robori-3dprinter/Mendel/OpenSCAD/prusa-i3-x-idler-1.stl

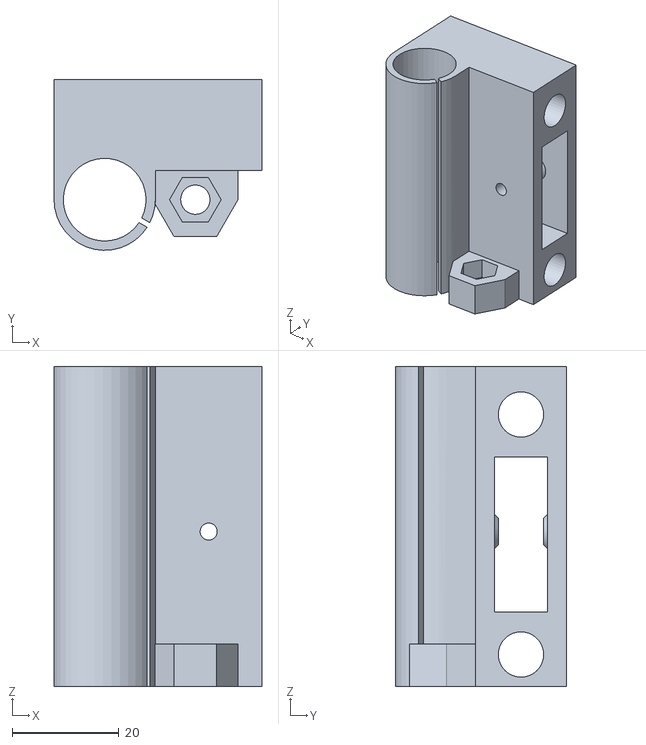
[picture p16: CAD file, 2015-08-26]
OpenSCAD/prusa-i3-x-idler-1.stl
39.0 x 32.0 x 60.0
