robori-3dprinter/Mendel/Printed Part/extruder-tongue-1x.stl

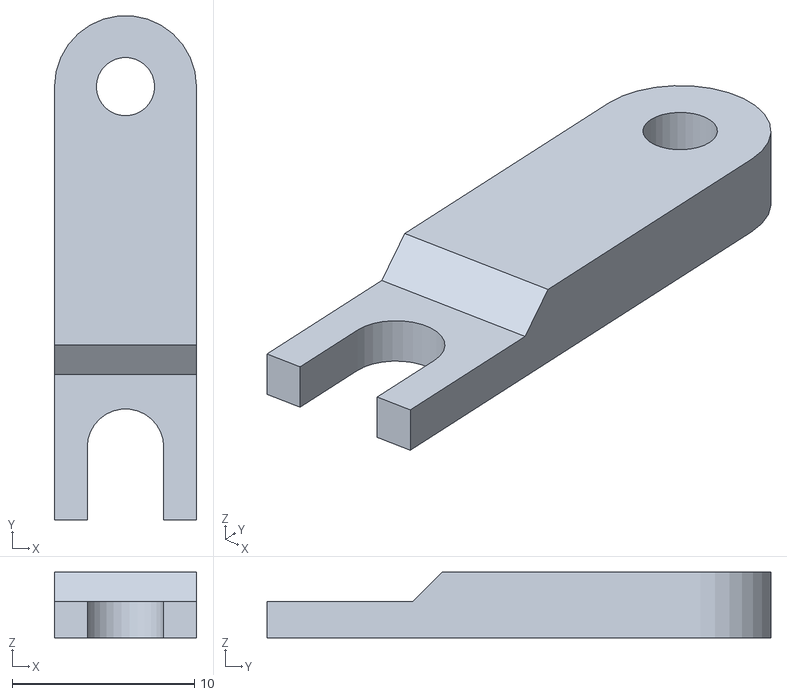
[picture p17: CAD file, 2015-08-26]
Printed Part/extruder-tongue-1x.stl
7.80 x 27.7 x 3.60
