robori-3dprinter/Mendel/OpenSCAD/vertex-body-hole-foot.dxf

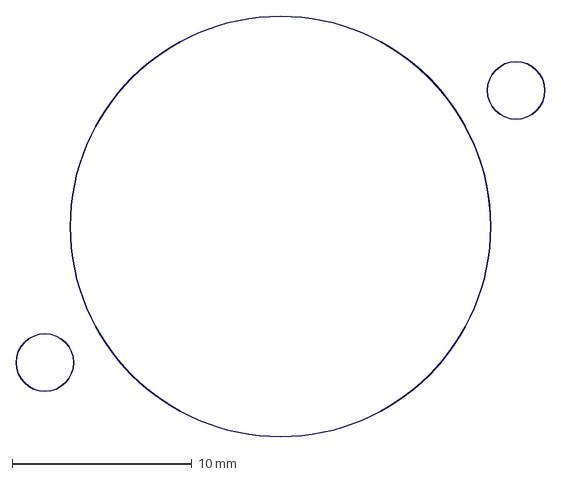
[picture p18: CAD file, 2015-08-26]
OpenSCAD/vertex-body-hole-foot.dxf
29.4 x 23.4 mm
