robori-3dprinter/Mendel/Printed Part/x-end-idler-1x.stl

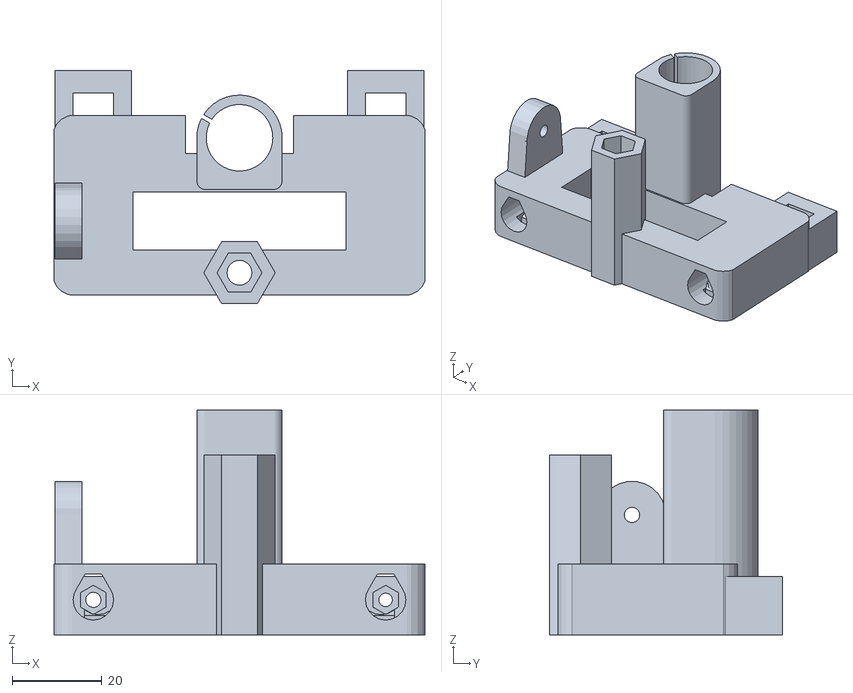
[picture p19: CAD file, 2015-08-26]
Printed Part/x-end-idler-1x.stl
82.5 x 51.9 x 50.0
