robori-3dprinter/Mendel/OpenSCAD/vertex-body-fixed-foot.dxf

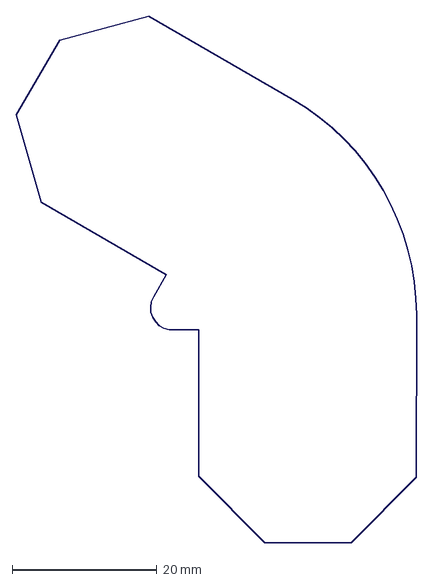
[picture p20: CAD file, 2015-08-26]
OpenSCAD/vertex-body-fixed-foot.dxf
55.4 x 72.9 mm
