robori-3dprinter/Mendel/Printed Part/extruder-large-gear-1x.stl

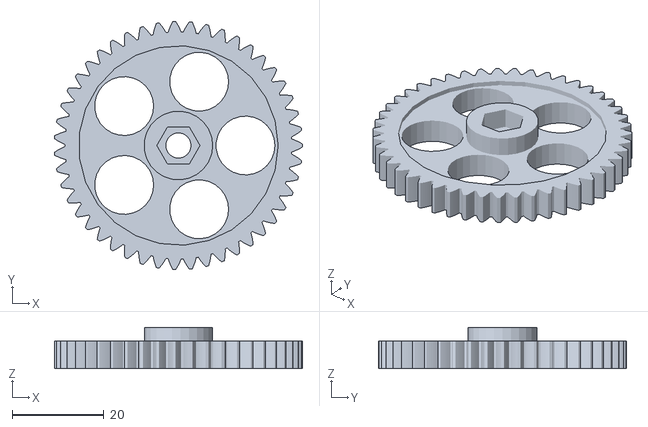
[picture p21: CAD file, 2015-08-26]
Printed Part/extruder-large-gear-1x.stl
54.2 x 54.2 x 9.00
