robori-3dprinter/Mendel/OpenSCAD/reprappro-small-gear-1off.stl

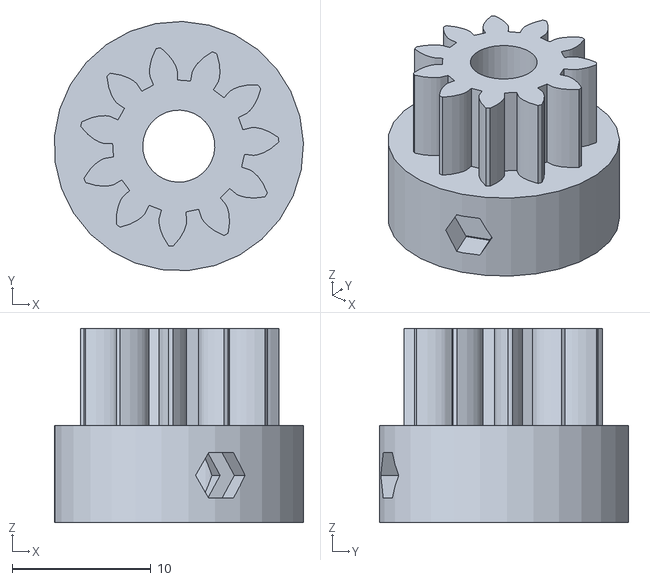
[picture p22: CAD file, 2015-08-25]
OpenSCAD/reprappro-small-gear-1off.stl
18.0 x 18.0 x 14.0
