robori-3dprinter/Mendel/Printed Part/x-carriage-1x.stl

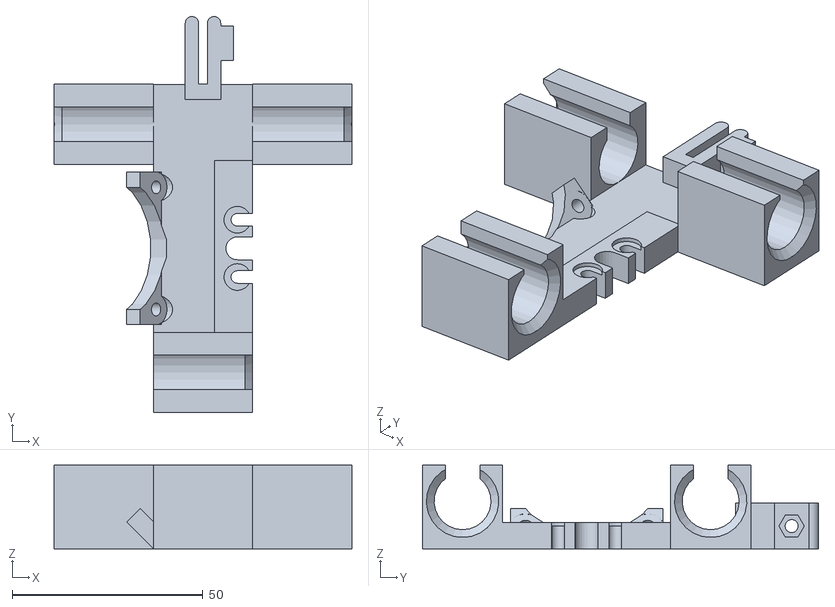
[picture p23: CAD file, 2015-08-26]
Printed Part/x-carriage-1x.stl
78.0 x 103.7 x 22.0
