robori-3dprinter/Mendel/Printed Part/pcb-clamp-bottom-1x.stl

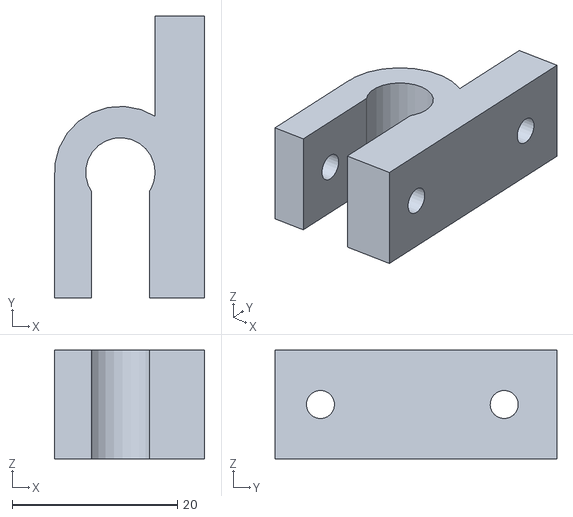
[picture p25: CAD file, 2015-08-26]
Printed Part/pcb-clamp-bottom-1x.stl
18.2 x 34.1 x 13.2
