robori-3dprinter/Mendel/Printed Part/filament-holder-clamp-front-2x.stl

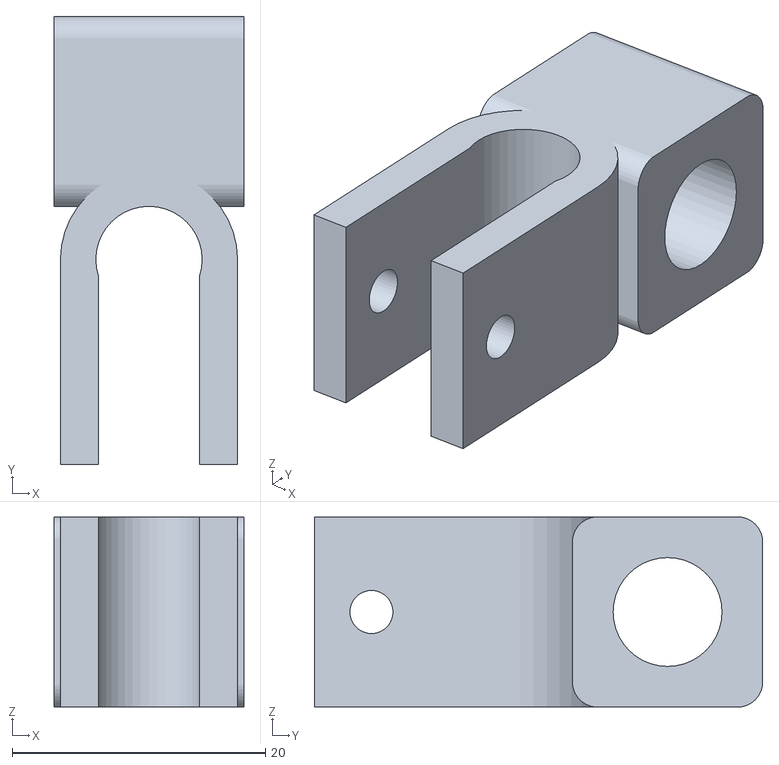
[picture p26: CAD file, 2015-08-26]
Printed Part/filament-holder-clamp-front-2x.stl
15.0 x 35.4 x 15.0
