robori-3dprinter/Mendel/Printed Part/extruder-bearing-cover-1x.stl

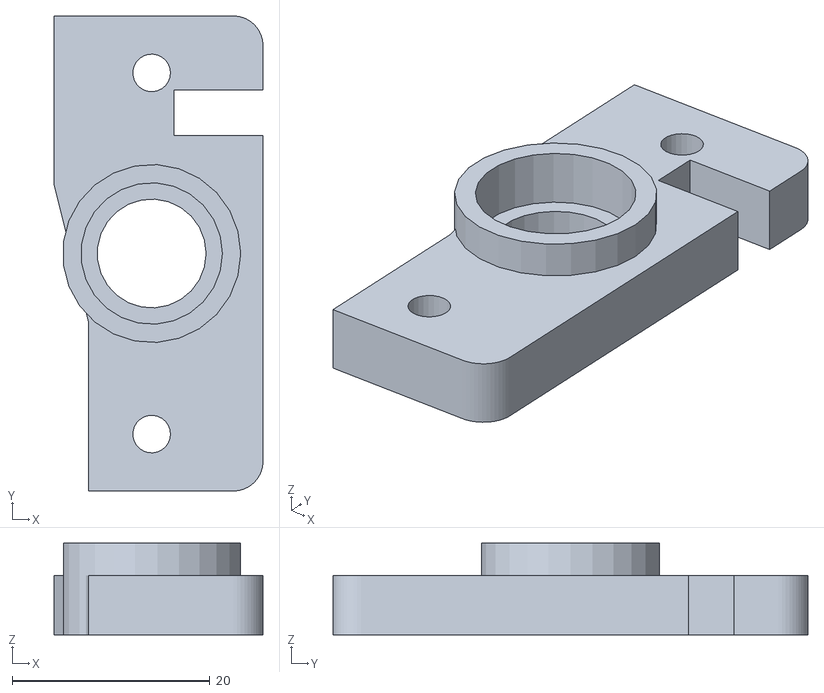
[picture p27: CAD file, 2015-08-26]
Printed Part/extruder-bearing-cover-1x.stl
21.1 x 48.0 x 9.25
