robori-3dprinter/Mendel/Printed Part/x-end-motor-1x.stl

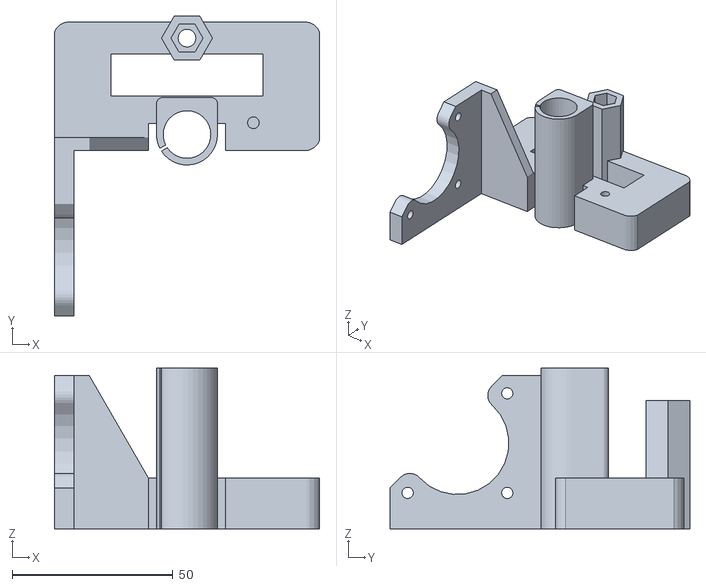
[picture p28: CAD file, 2015-08-26]
Printed Part/x-end-motor-1x.stl
82.5 x 93.4 x 50.0
