robori-3dprinter/Mendel/Printed Part/pcb-fan-holder-1x.stl

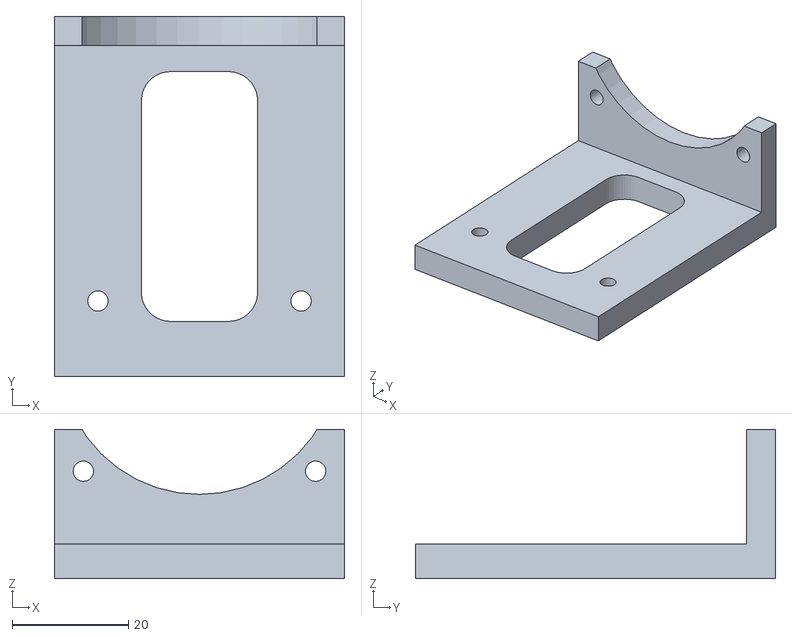
[picture p29: CAD file, 2015-08-26]
Printed Part/pcb-fan-holder-1x.stl
50.0 x 62.0 x 25.7
