robori-3dprinter/Mendel/Printed Part/lcd-clamp-left-1x.stl

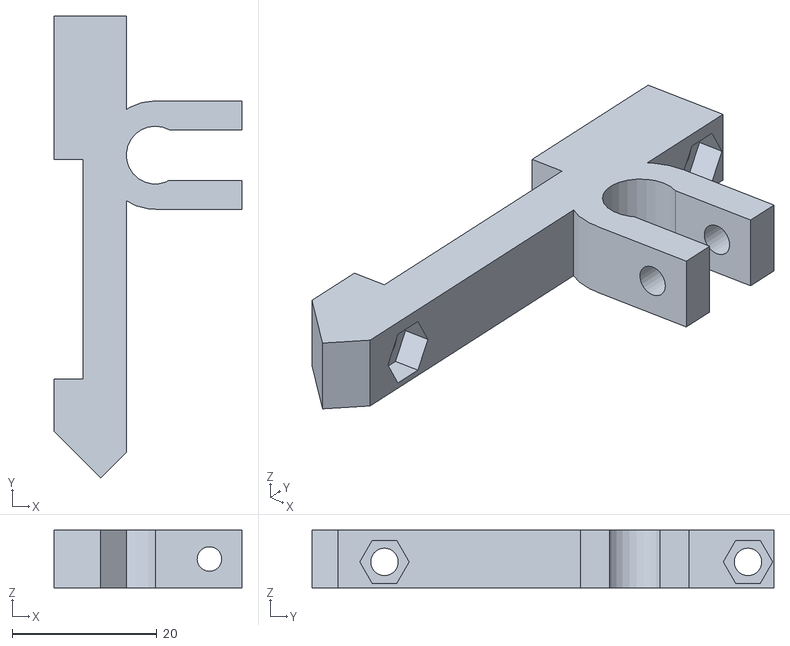
[picture p30: CAD file, 2015-08-26]
Printed Part/lcd-clamp-left-1x.stl
26.0 x 63.9 x 8.00
