robori-3dprinter/Mendel/Printed Part/y-motor-mount-1x.stl

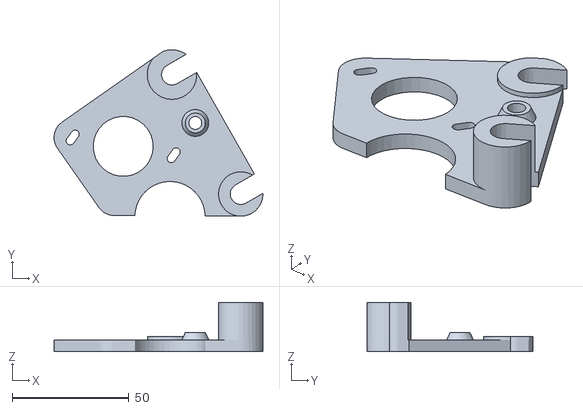
[picture p31: CAD file, 2015-08-26]
Printed Part/y-motor-mount-1x.stl
89.3 x 71.2 x 21.0
