robori-3dprinter/Mendel/Printed Part/pcb-clamp-top-1x.stl

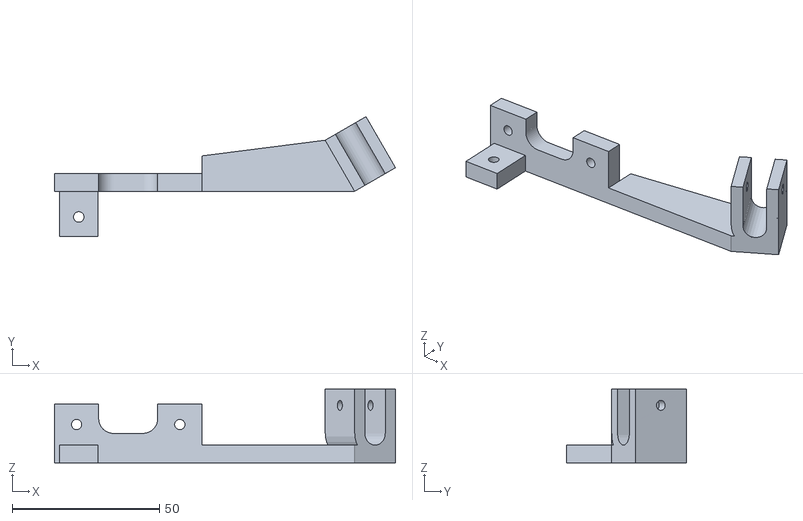
[picture p32: CAD file, 2015-08-26]
Printed Part/pcb-clamp-top-1x.stl
115.7 x 40.6 x 25.0
