robori-3dprinter/Mendel/Printed Part/extruder-retainer-1x.stl

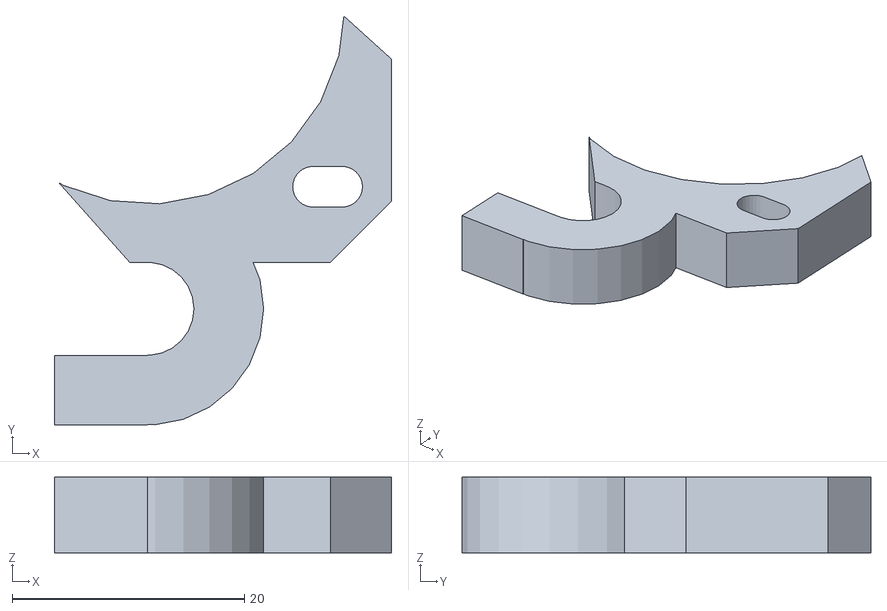
[picture p33: CAD file, 2015-08-26]
Printed Part/extruder-retainer-1x.stl
29.0 x 35.2 x 6.50
