robori-3dprinter/Mendel/Printed Part/lcd-clamp-right-1x.stl

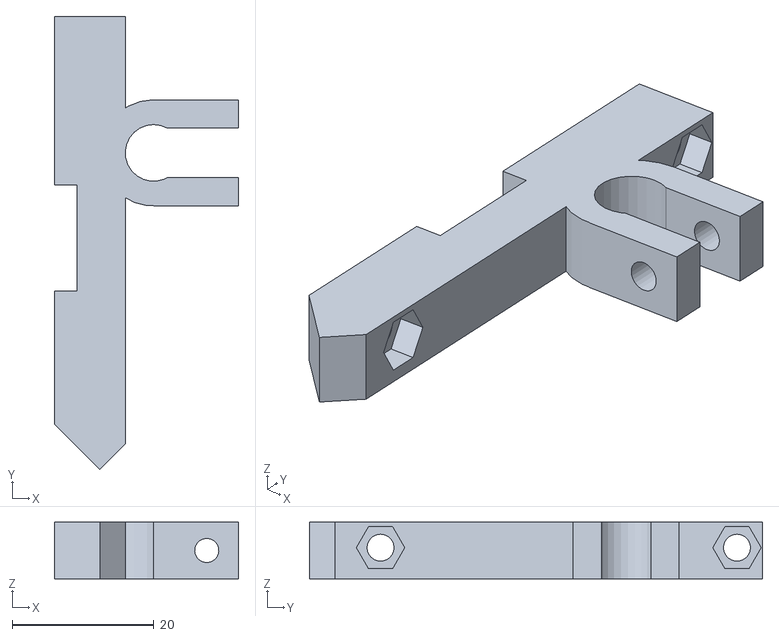
[picture p34: CAD file, 2015-08-26]
Printed Part/lcd-clamp-right-1x.stl
26.0 x 63.9 x 8.00
