robori-3dprinter/Mendel/Printed Part/pcb-clamp-corner-1x.stl

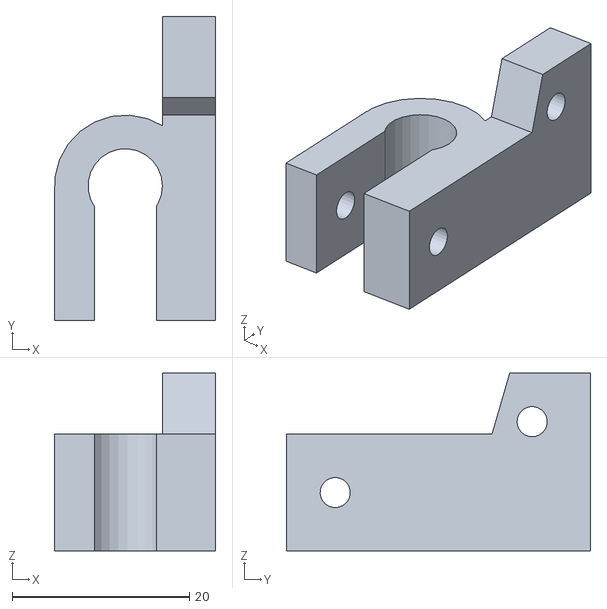
[picture p35: CAD file, 2015-08-26]
Printed Part/pcb-clamp-corner-1x.stl
18.2 x 34.3 x 20.1
