robori-3dprinter/Mendel/Printed Part/psu-cover-1x.stl

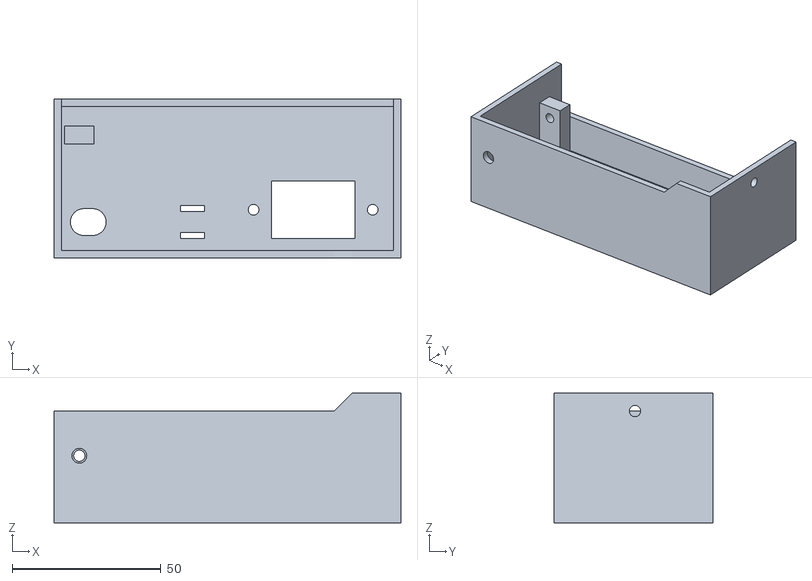
[picture p36: CAD file, 2015-08-23]
Printed Part/psu-cover-1x.stl
116.5 x 53.3 x 43.5
