robori-3dprinter/Mendel/Printed Part/extruder-idler-1x.stl

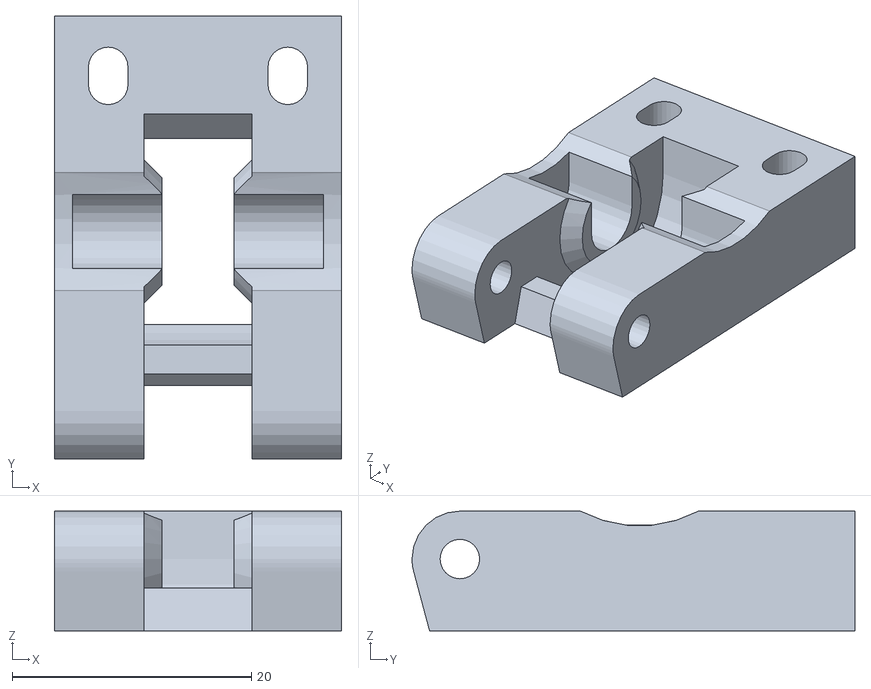
[picture p37: CAD file, 2015-08-23]
Printed Part/extruder-idler-1x.stl
24.0 x 37.0 x 10.0
