robori-3dprinter/Mendel/Printed Part/x-belt-guide-1x.stl

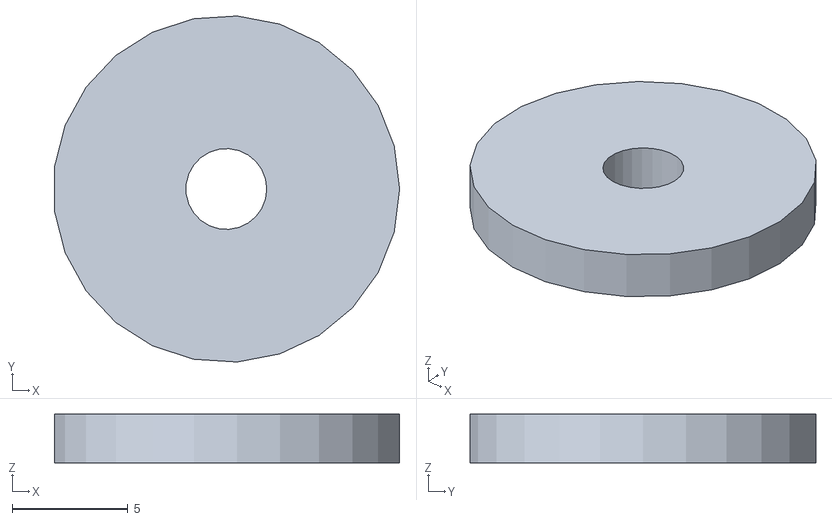
[picture p38: CAD file, 2015-08-23]
Printed Part/x-belt-guide-1x.stl
14.9 x 15.0 x 2.10
