robori-3dprinter/Mendel/Printed Part/y-belt-guide-4x.stl

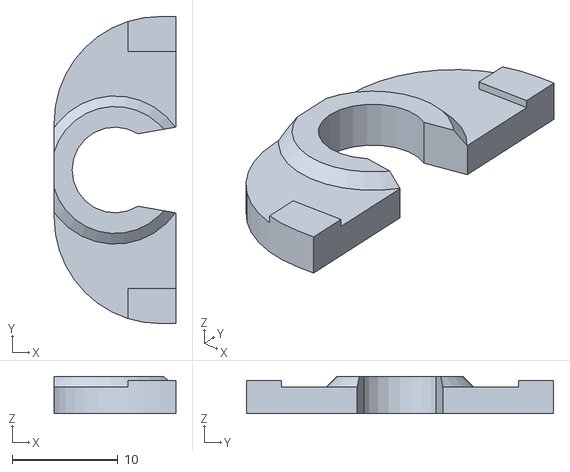
[picture p39: CAD file, 2015-08-23]
Printed Part/y-belt-guide-4x.stl
11.5 x 29.0 x 3.50
