robori-3dprinter/Mendel/Printed Part/filament-holder-end-2x.stl

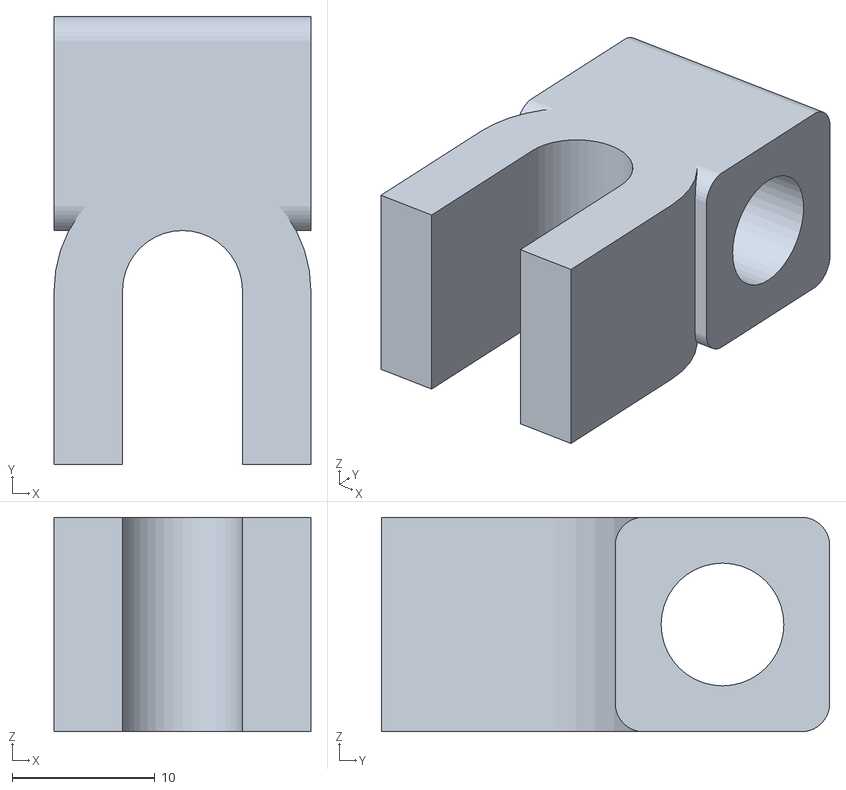
[picture p40: CAD file, 2015-08-23]
Printed Part/filament-holder-end-2x.stl
18.0 x 31.4 x 15.0
