robori-3dprinter/Mendel/Printed Part/filament-holder-clamp-rear-2x.stl

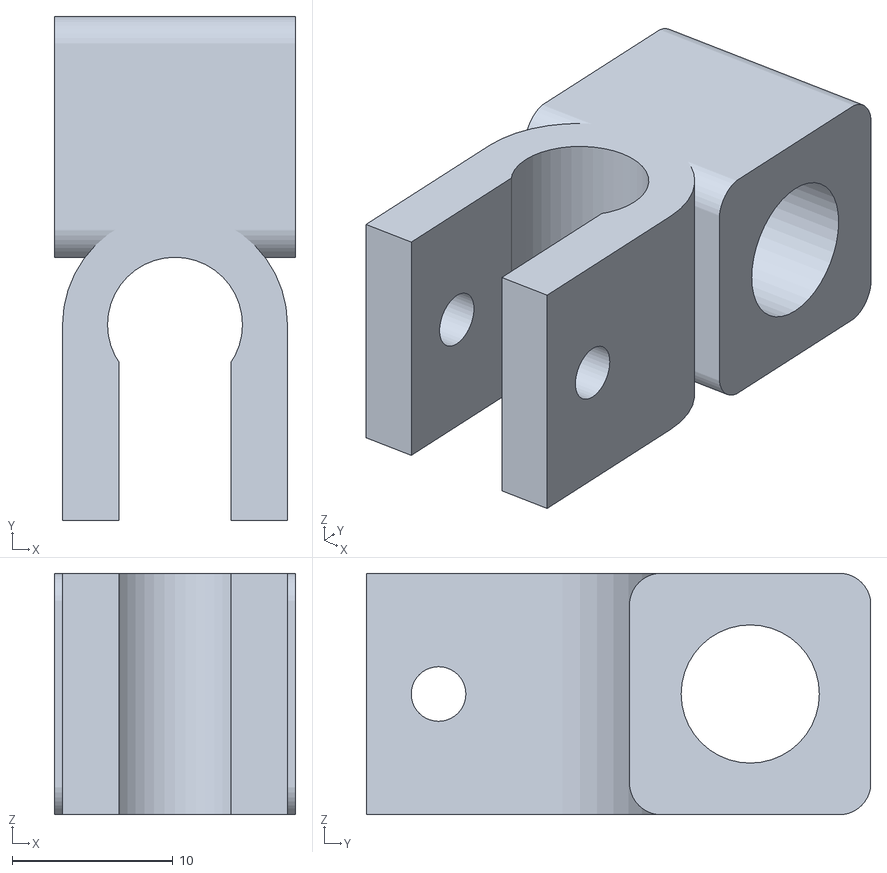
[picture p41: CAD file, 2015-08-23]
Printed Part/filament-holder-clamp-rear-2x.stl
15.0 x 31.4 x 15.0
