robori-3dprinter/Mendel/Printed Part/y-bearing-holder-3x.stl

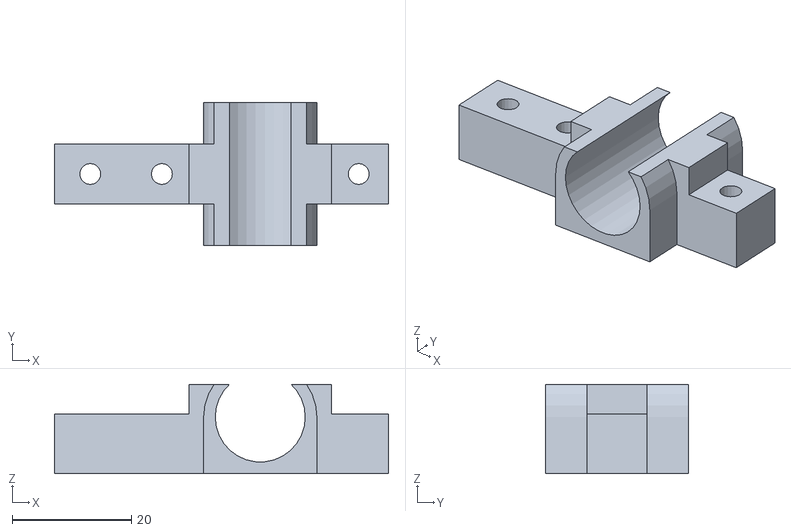
[picture p42: CAD file, 2015-08-23]
Printed Part/y-bearing-holder-3x.stl
56.0 x 24.0 x 15.0
