robori-3dprinter/Mendel/Printed Part/y-belt-clamp-2x.stl

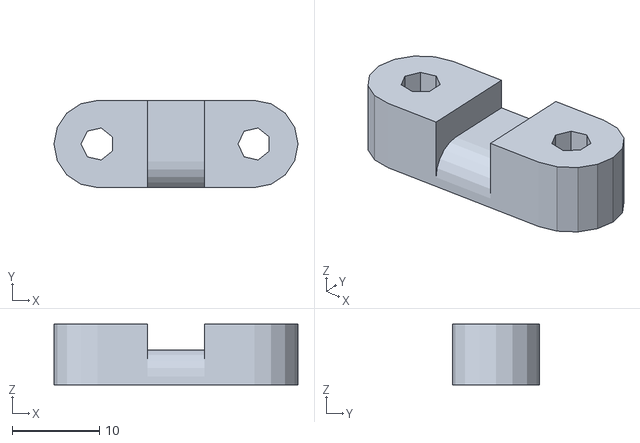
[picture p43: CAD file, 2015-08-23]
Printed Part/y-belt-clamp-2x.stl
28.0 x 10.0 x 7.00
