robori-3dprinter/Mendel/Printed Part/bar-clamp-8x.stl

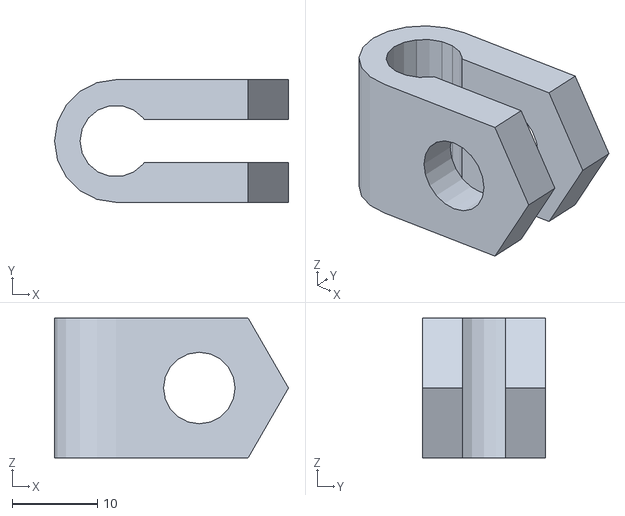
[picture p44: CAD file, 2015-08-23]
Printed Part/bar-clamp-8x.stl
27.5 x 14.4 x 16.4
