robori-3dprinter/Mendel/Printed Part/y-motor-spacer-1x.stl

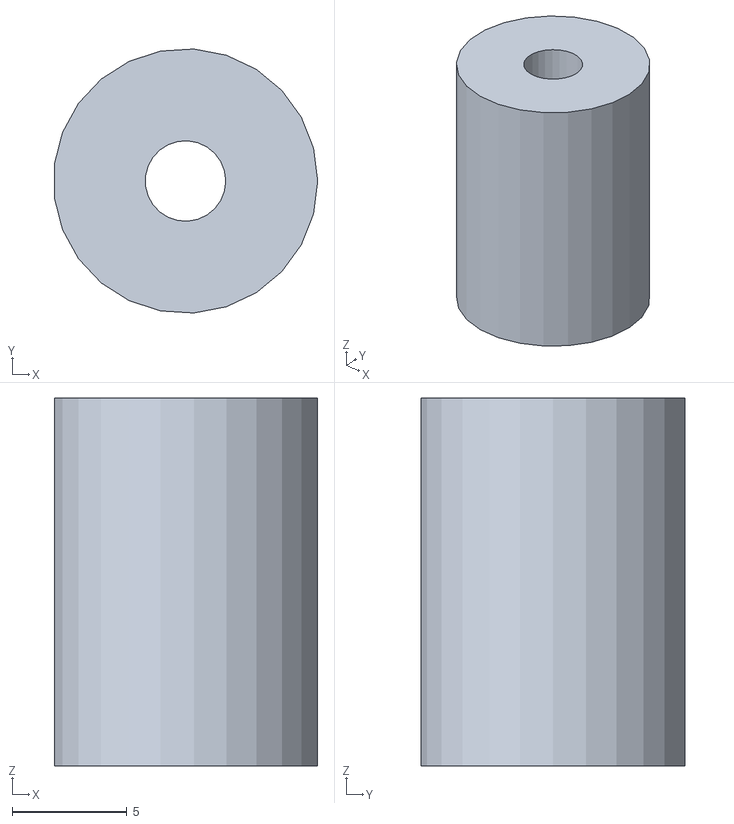
[picture p45: CAD file, 2015-08-23]
Printed Part/y-motor-spacer-1x.stl
11.5 x 11.5 x 16.0
