robori-3dprinter/Mendel/Printed Part/z-motor-mount-2x.stl

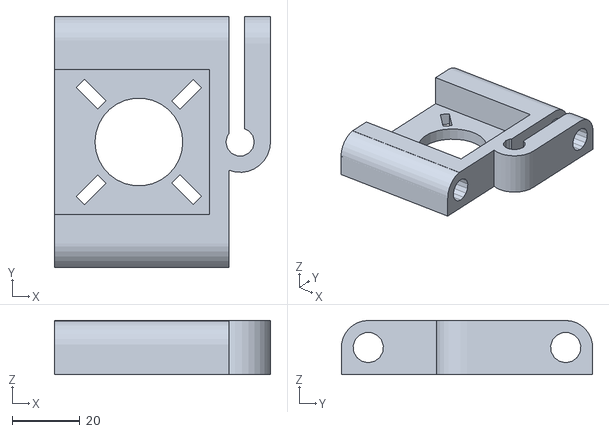
[picture p46: CAD file, 2015-08-23]
Printed Part/z-motor-mount-2x.stl
64.0 x 74.5 x 16.0
